bdlucas1/3d-casting/molds/benchyring-mold.3mf

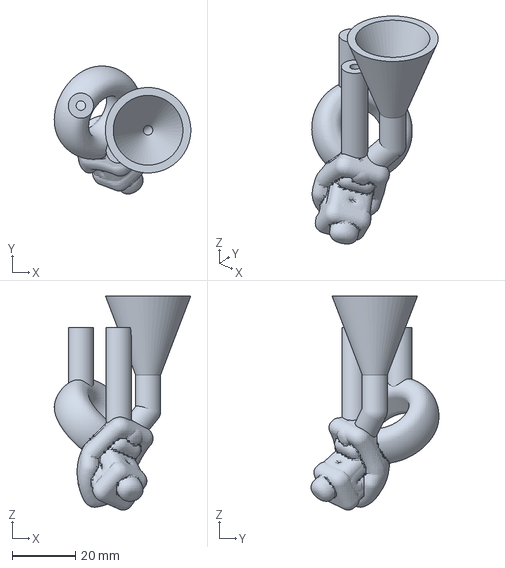
[picture p9: CAD file, 2025-03-09]
molds/benchyring-mold.3mf
43.3 x 40.6 x 67.9 mm
