bdlucas1/3d-casting/molds/butterfly-pendant.3mf

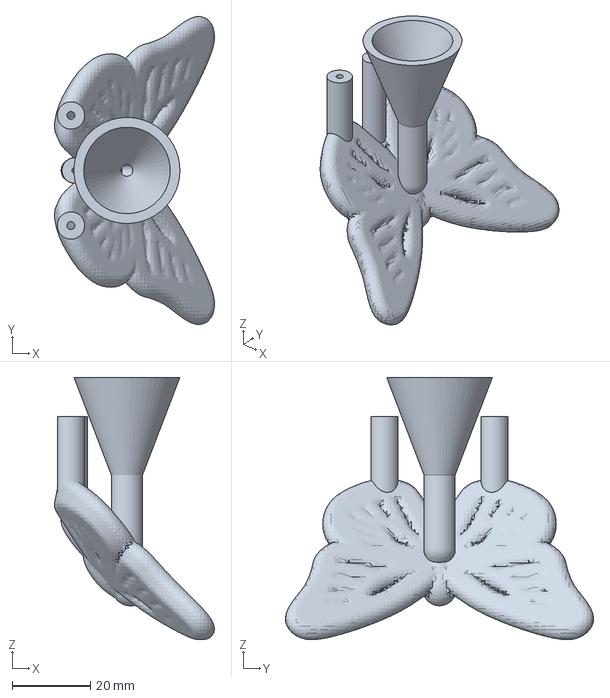
[picture p10: CAD file, 2025-03-09]
molds/butterfly-pendant.3mf
41.0 x 78.8 x 67.1 mm
