bdlucas1/3d-casting/molds/ring.3mf

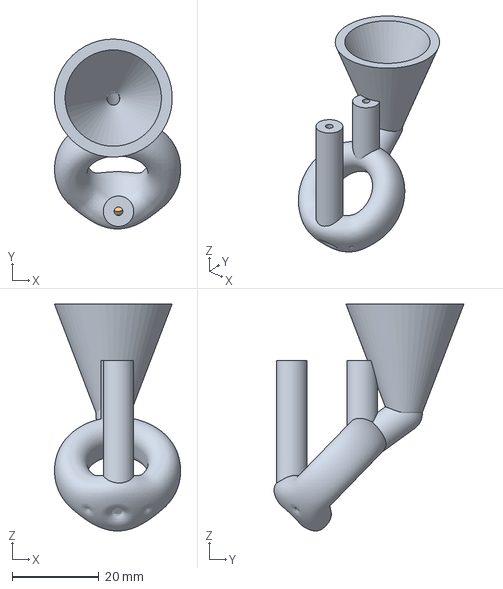
[picture p11: CAD file, 2025-03-09]
molds/ring.3mf
29.0 x 43.7 x 52.2 mm
mold
inset
