bdlucas1/3d-casting/molds/demon.3mf

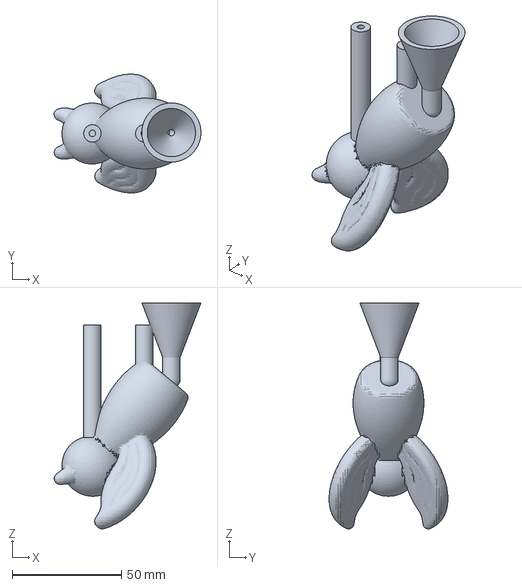
[picture p12: CAD file, 2025-02-02]
molds/demon.3mf
67.3 x 54.5 x 103.6 mm
