bdlucas1/3d-casting/molds/chess-bishop.3mf

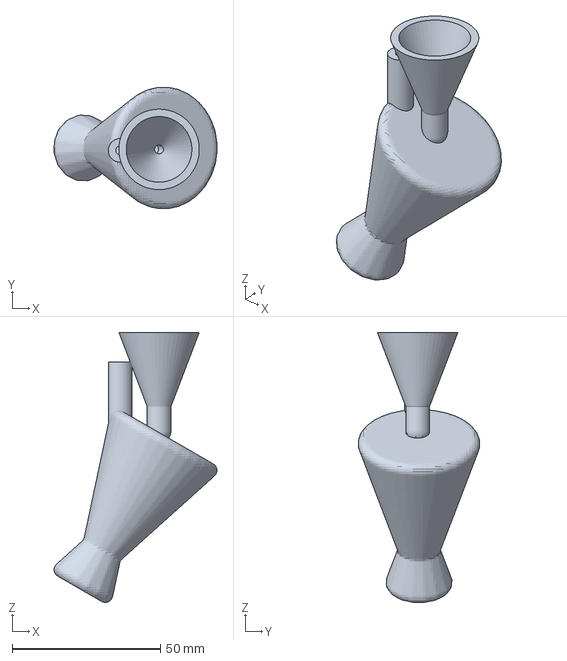
[picture p13: CAD file, 2025-02-01]
molds/chess-bishop.3mf
54.9 x 40.9 x 91.0 mm
