bdlucas1/3d-casting/molds/chess-knight.3mf

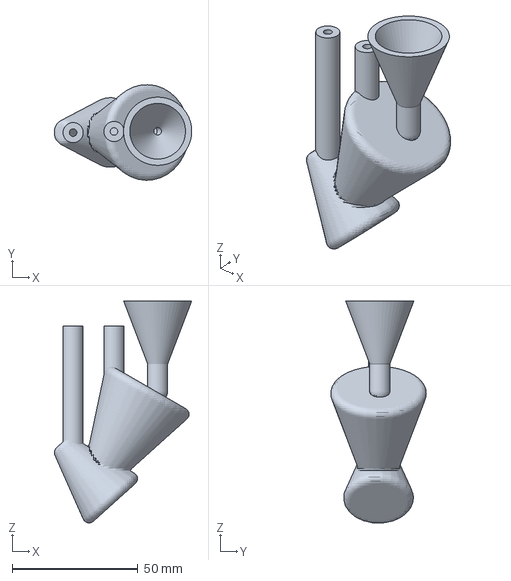
[picture p14: CAD file, 2025-02-01]
molds/chess-knight.3mf
54.6 x 38.0 x 88.3 mm
