bdlucas1/3d-casting/molds/chess-rook.3mf

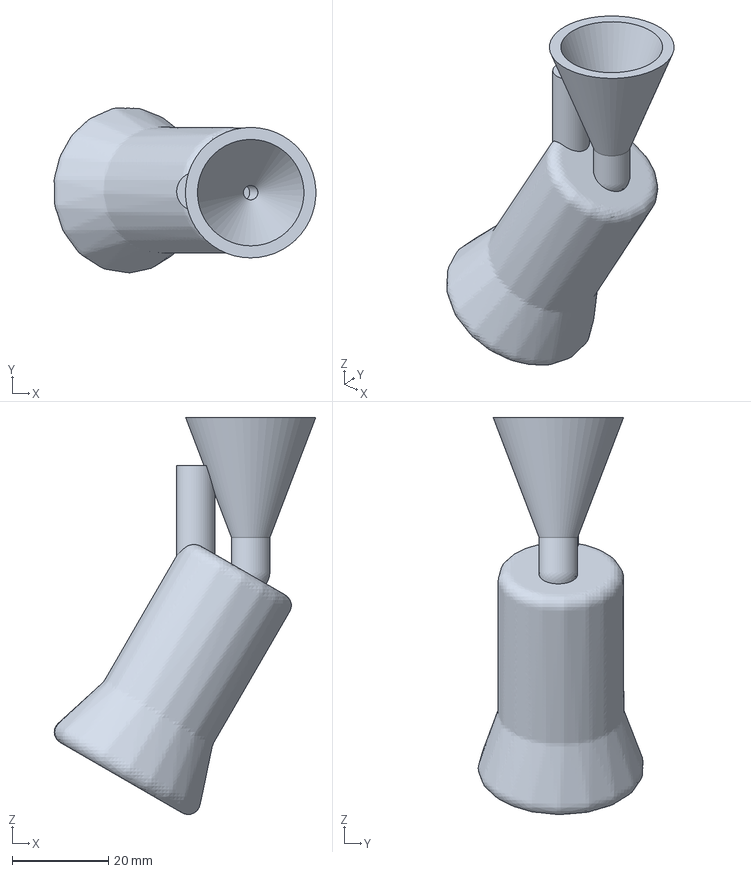
[picture p15: CAD file, 2025-02-01]
molds/chess-rook.3mf
54.4 x 34.3 x 82.6 mm
