bdlucas1/3d-casting/molds/chess-pawn.3mf

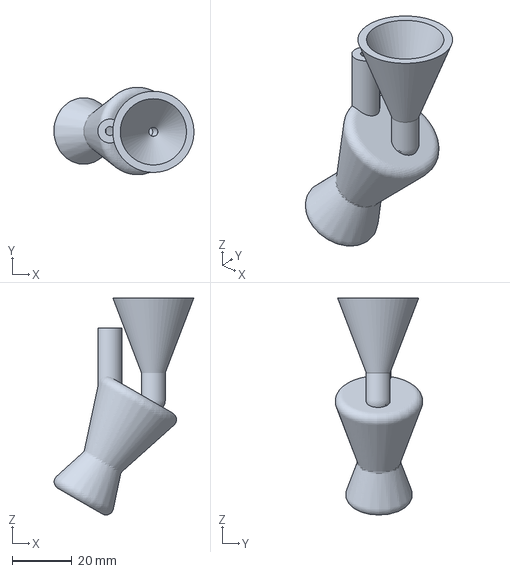
[picture p16: CAD file, 2025-02-01]
molds/chess-pawn.3mf
46.7 x 29.2 x 72.5 mm
