bdlucas1/3d-casting/molds/chess-king-hollow.3mf

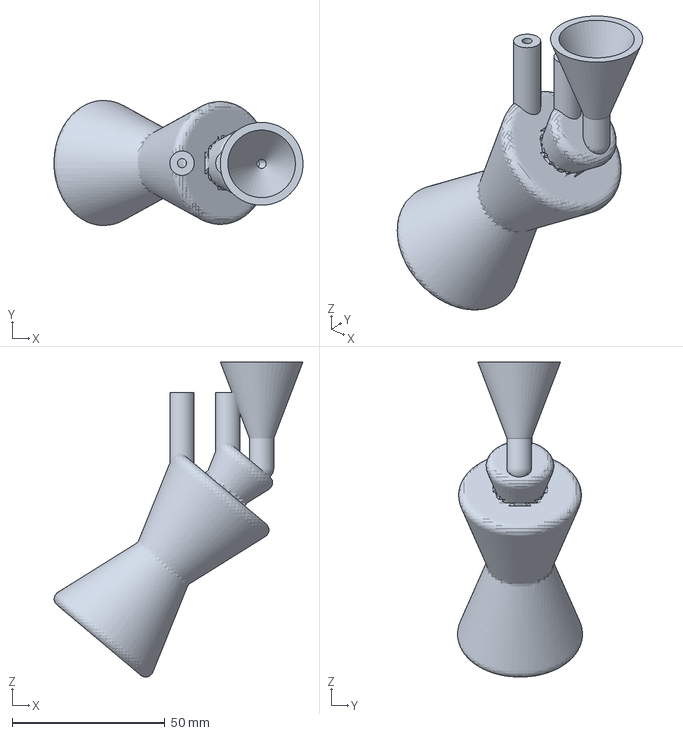
[picture p17: CAD file, 2025-02-01]
molds/chess-king-hollow.3mf
81.6 x 41.0 x 103.2 mm
