bdlucas1/3d-casting/molds/chess-queen-hollow.3mf

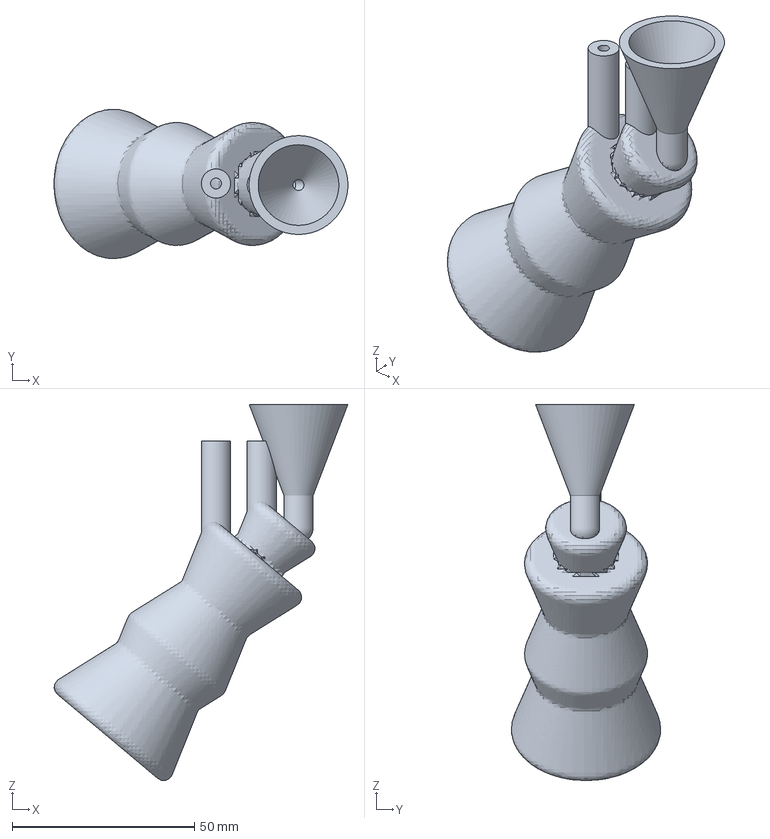
[picture p18: CAD file, 2025-01-31]
molds/chess-queen-hollow.3mf
80.6 x 40.9 x 103.2 mm
