bdlucas1/3d-casting/molds/chess-queen.3mf

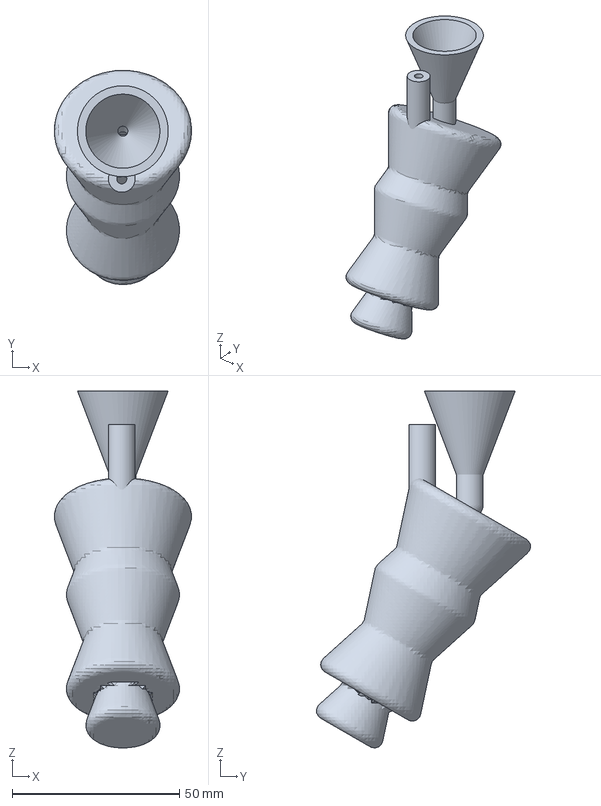
[picture p19: CAD file, 2025-01-31]
molds/chess-queen.3mf
41.0 x 64.0 x 106.6 mm
