bdlucas1/3d-casting/molds/knot_4_1-ribbon.3mf

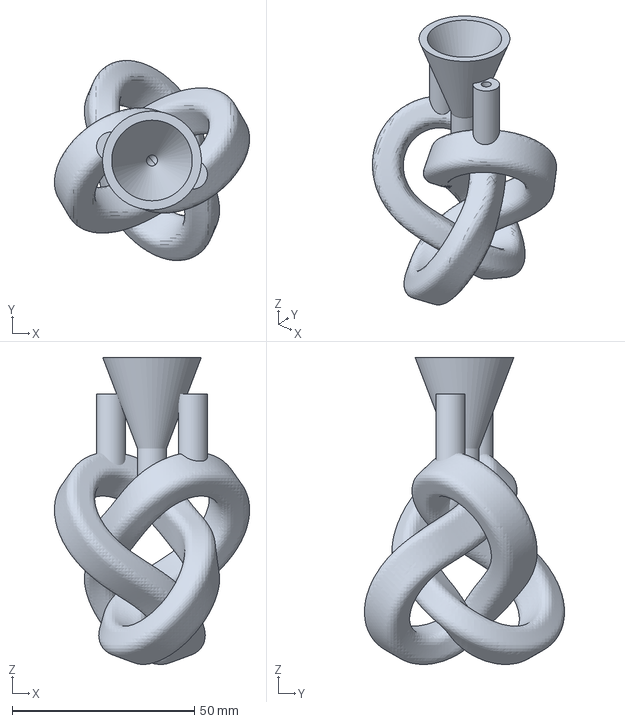
[picture p20: CAD file, 2025-01-19]
molds/knot_4_1-ribbon.3mf
53.6 x 55.0 x 84.3 mm
