bdlucas1/3d-casting/molds/butterfly.3mf

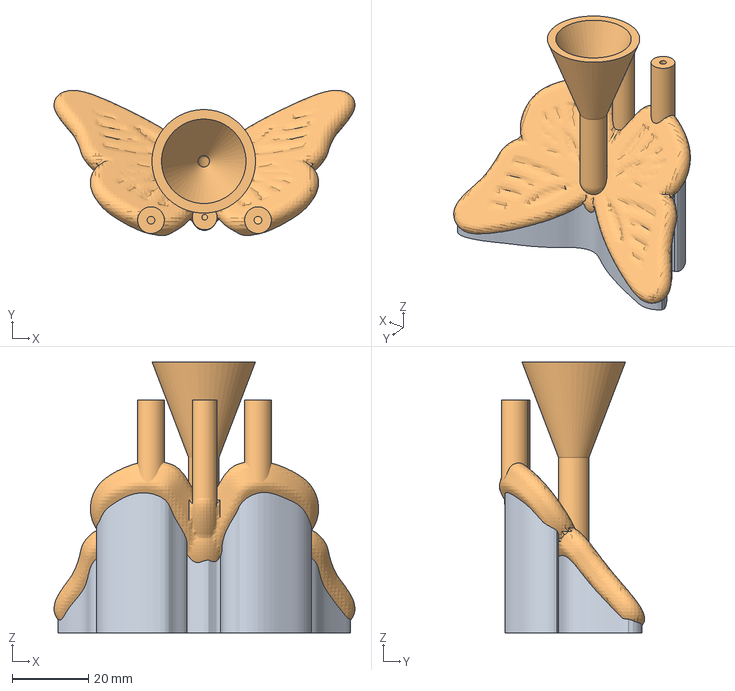
[picture p21: CAD file, 2025-01-19]
molds/butterfly.3mf
78.9 x 38.1 x 71.0 mm
support
mold
