bdlucas1/3d-casting/molds/knot_4_1-tube.3mf

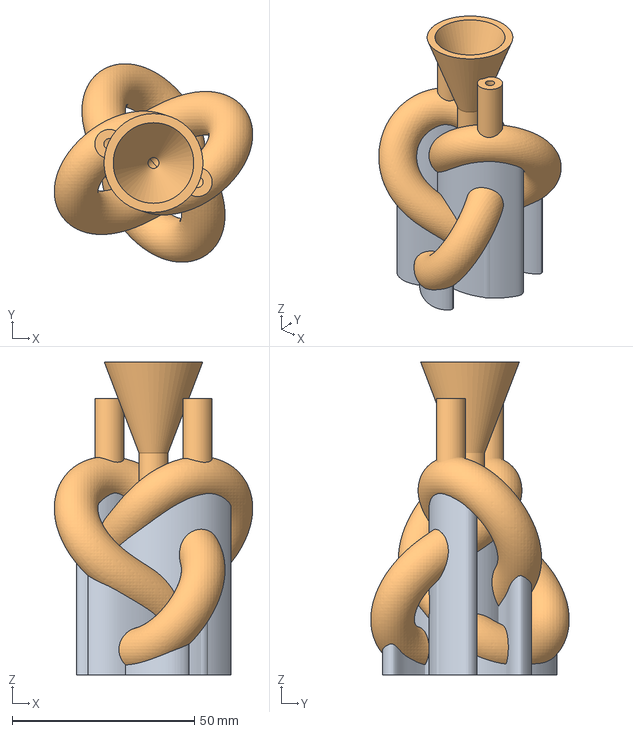
[picture p22: CAD file, 2025-01-19]
molds/knot_4_1-tube.3mf
54.5 x 54.5 x 86.0 mm
support
mold
