bdlucas1/3d-casting/molds/cubes.3mf

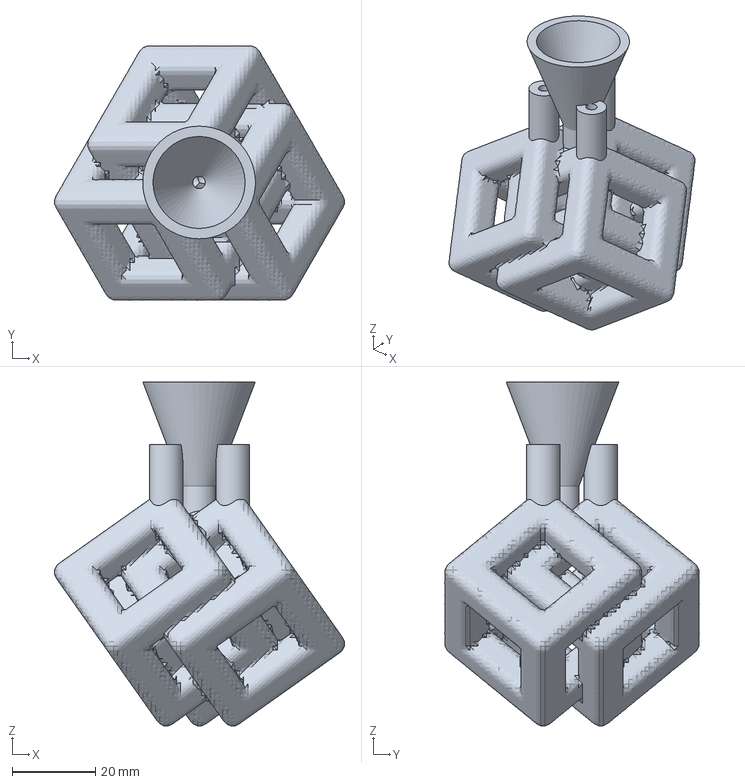
[picture p23: CAD file, 2025-01-19]
molds/cubes.3mf
69.8 x 61.3 x 82.8 mm
