bdlucas1/3d-casting/molds/knot_3_1-ribbon-slice.3mf

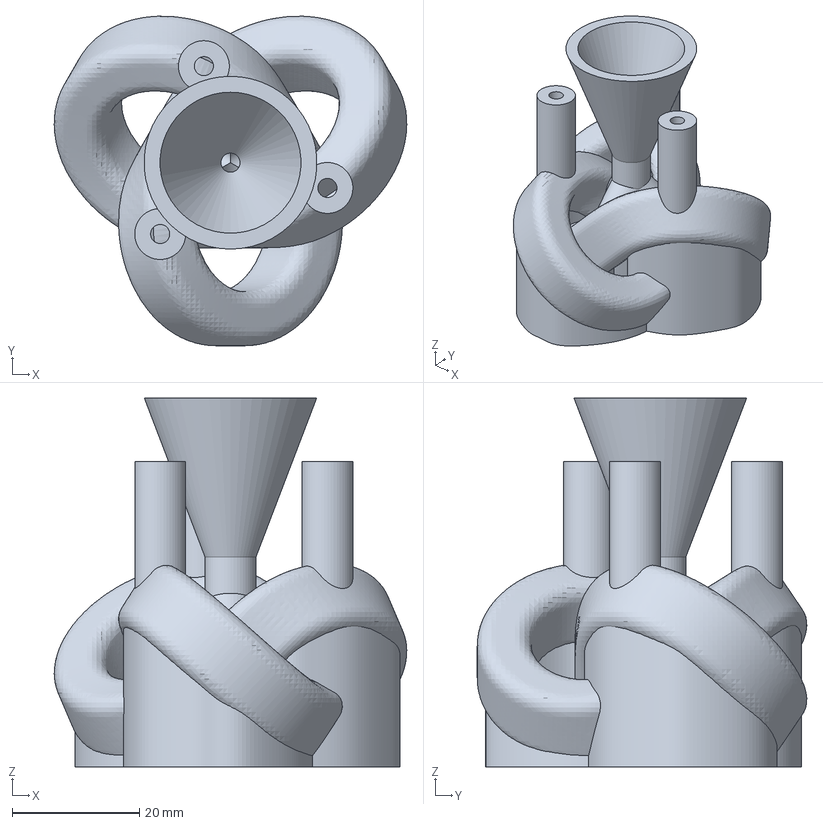
[picture p24: CAD file, 2025-01-19]
molds/knot_3_1-ribbon-slice.3mf
55.4 x 51.8 x 57.9 mm
