bdlucas1/3d-casting/molds/dev.3mf

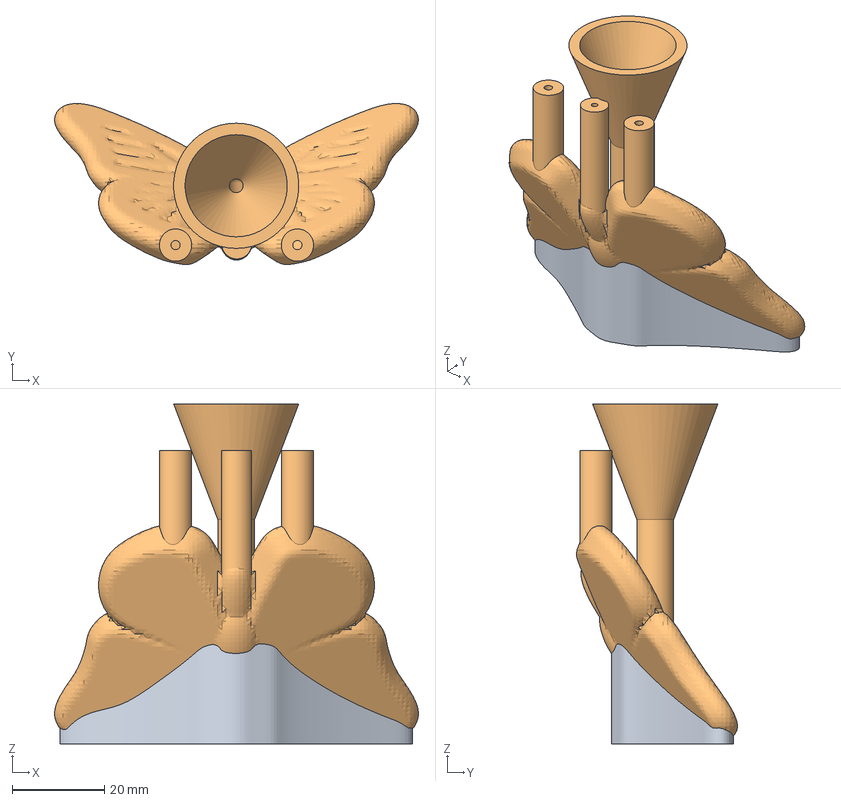
[picture p25: CAD file, 2025-01-19]
molds/dev.3mf
78.9 x 34.9 x 73.6 mm
support
mold
