bdlucas1/3d-casting/molds/bunny-hollow.3mf

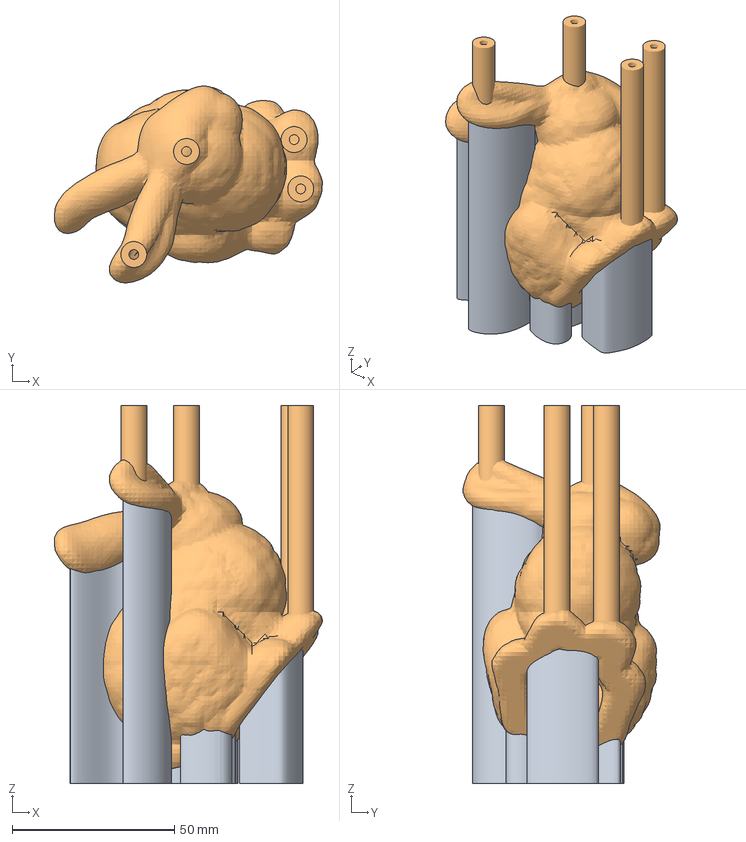
[picture p26: CAD file, 2025-01-19]
molds/bunny-hollow.3mf
82.7 x 60.8 x 116.6 mm
support
mold
