bdlucas1/3d-casting/molds/rings.3mf

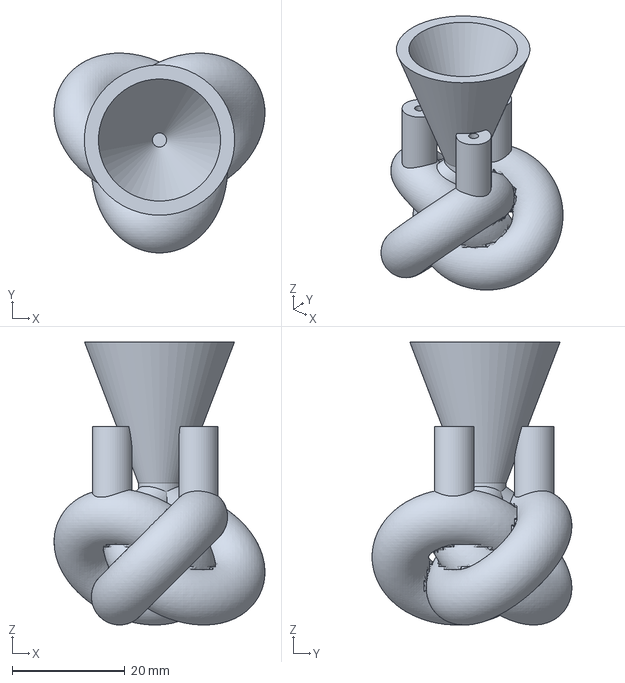
[picture p27: CAD file, 2025-01-19]
molds/rings.3mf
37.3 x 35.4 x 50.1 mm
