bdlucas1/3d-casting/molds/bunny.3mf

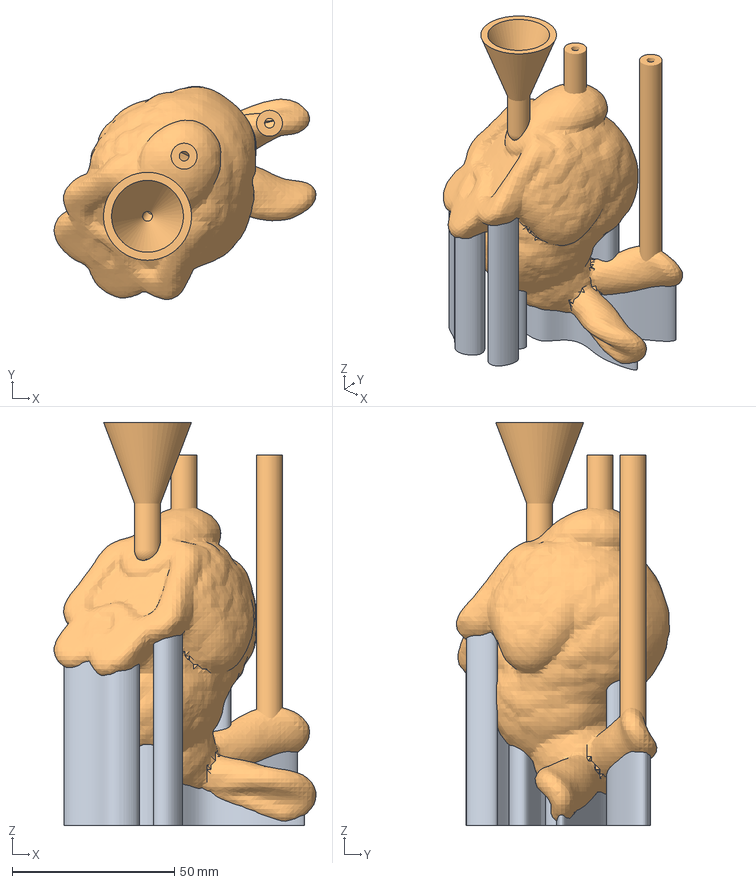
[picture p28: CAD file, 2025-01-19]
molds/bunny.3mf
80.7 x 65.7 x 124.2 mm
support
mold
