bdlucas1/3d-casting/molds/butterfly-150.3mf

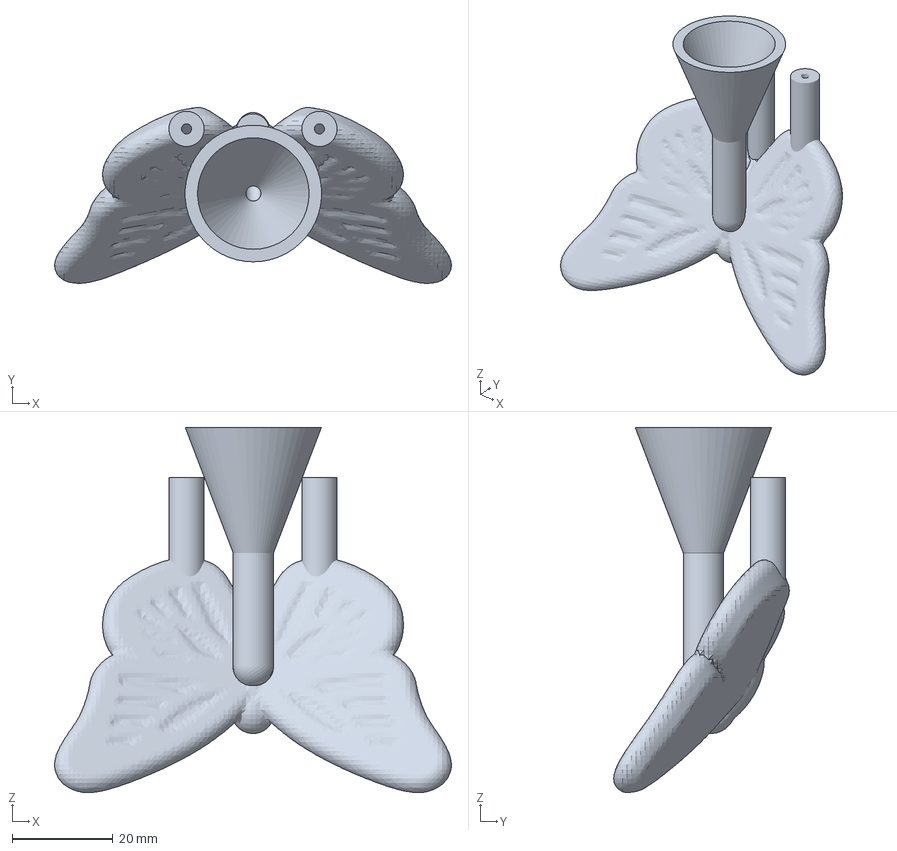
[picture p29: CAD file, 2025-01-19]
molds/butterfly-150.3mf
78.9 x 34.9 x 72.6 mm
