bdlucas1/3d-casting/molds/knot_5_2-tube.3mf

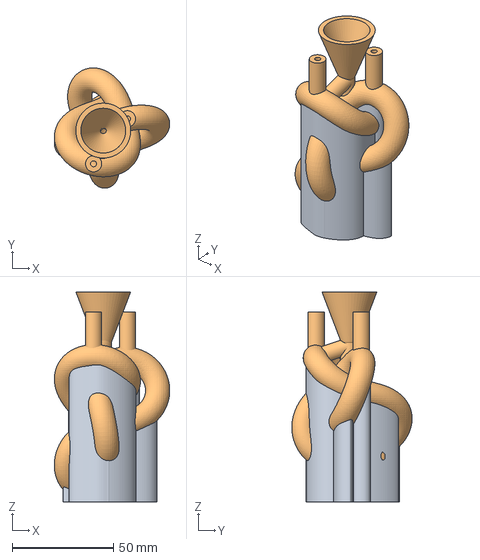
[picture p30: CAD file, 2025-01-19]
molds/knot_5_2-tube.3mf
57.1 x 59.5 x 103.8 mm
support
mold
