bdlucas1/3d-casting/molds/knot_5_1-tube.3mf

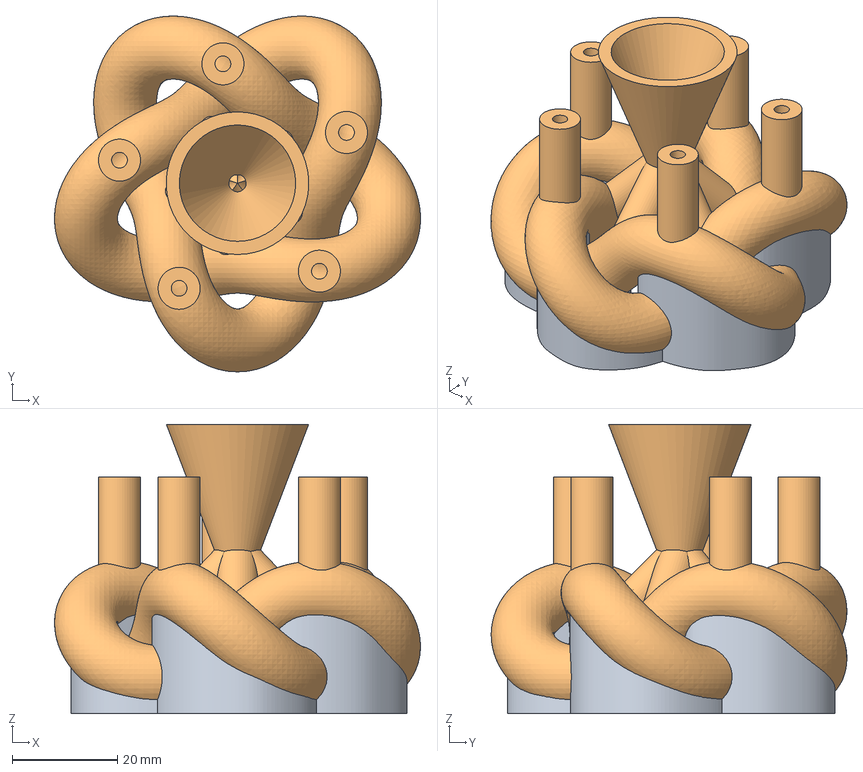
[picture p31: CAD file, 2025-01-19]
molds/knot_5_1-tube.3mf
69.7 x 67.7 x 55.0 mm
support
mold
