bdlucas1/3d-casting/molds/knot_3_1-tube.3mf

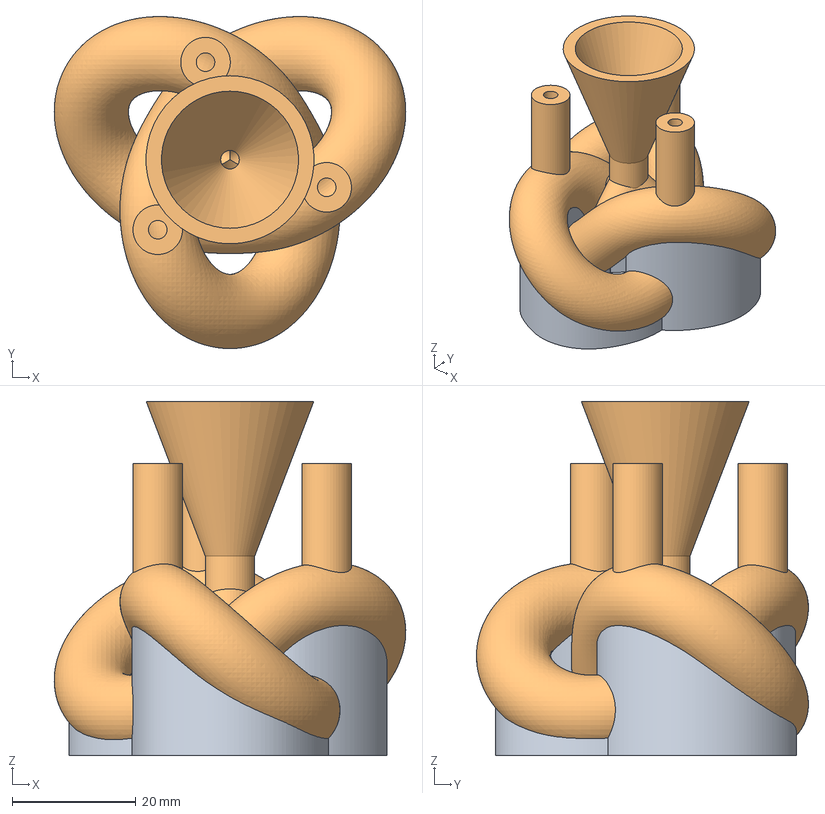
[picture p32: CAD file, 2025-01-19]
molds/knot_3_1-tube.3mf
56.8 x 53.6 x 57.2 mm
support
mold
